Startrekker007/ECEN405DClass/LTSpice/triangle2.asc

C1: cap; 5n
C2: cap; 10µ
C3: cap; 100µ
R1: res; 8.2k
R2: res; 10k
R3: res; 10k
R4: res; 30k
R5: res; 1k
R6: res; 10k
R7: res; 10k
R8: res; 4k
R9: res; 1k
R10: res; 4k
R11: res; 1k
U1: LTC1051A
U2: LTC1051A
U3: LT1018
V1: voltage; 5
V2: voltage; SINE(0 1 20)
Named nets: 0, +5, +REF, +IN
.tran 0 0.6 0.5 0.001 startup
