Startrekker007/ECEN405DClass/LTSpice/Triangle1.asc

C1: cap; 10n
C2: cap; 10n
R1: res; 8k
R2: res; 1k
R3: res; 200k
R4: res; 40k
U1: AD823
U2: AD823
U3: AD823
V1: voltage; 5
Named nets: 0, +5
.tran 0 1 0.9 0.01 startup
