Startrekker007/ECEN405DClass/LTSpice/InputFilter.asc

C1: cap; 100n
C2: cap; 1.8µ
C3: cap; 100n
C4: cap; 1µ
C5: cap; 5.6µ
C6: cap; 3.3µ
R1: res; 2.7k
R2: res; 1.3k
R3: res; 16k
R4: res; 8.2k
R5: res; 15k
R6: res; 910
U1: AD8565
U2: AD8565
U3: AD8565
U4: AD8565
U5: AD8565
V1: voltage; 18
V2: voltage; 18
V3: voltage; AC 1
Named nets: 0, V+, V-
.ac dec 10 1 20000
