Startrekker007/ECEN405DClass/Altium_Kicad/Kicad/PWM/pwm/pwm.sch

## KiCad design Altium_Kicad/Kicad/PWM/pwm/pwm.sch (2020-03-15, an earlier design)

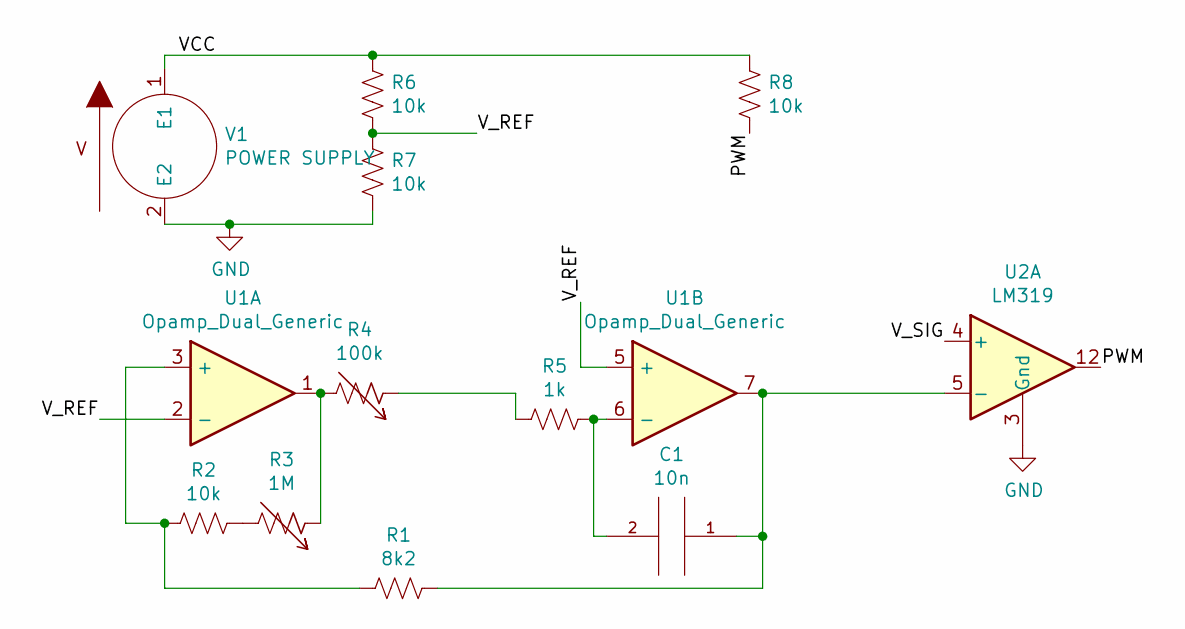
[picture p13: schematic pwm.sch]

Parts:
C1: 10n
R1: 8k2
R2, R6, R7, R8: 10k
R3: 1M
R4: 100k
R5: 1k
U1: Opamp_Dual_Generic
U2: LM319
V1: POWER SUPPLY

Connections:
GND: R7.2, U2.3 (Gnd), V1.2 (E2)
unnamed: C1.1, R1.1, U1.7, U2.5 (-)
unnamed: C1.2, R5.1, U1.6 (-)
unnamed: R1.2, R2.2, U1.3 (+)
unnamed: R2.1, R3.2
unnamed: R3.1, R4.2, U1.1
unnamed: R4.1, R5.2
PWM: R8.2, U2.12
VCC: R6.1, R8.1, V1.1 (E1)
V_REF: R6.2, R7.1, U1.2 (-), U1.5 (+)
V_SIG: U2.4 (+)
